relativty/Relativty/ressources/img/headset.jpg

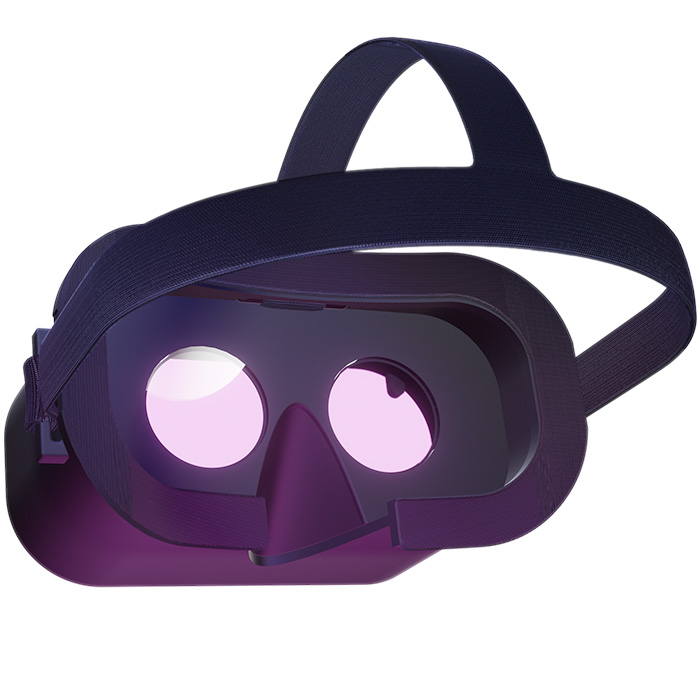
ressources/img/headset.jpg
