relativty/Relativty/Relativty_Driver/include/Relativty_HMDDriver.hpp

// Copyright (C) 2020  Max Coutte, Gabriel Combe
// Copyright (C) 2020  Relativty.com
//
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
#pragma once
#include <thread>
#include <atomic>
#include <WinSock2.h>
#include "hidapi/hidapi.h"
#include "openvr_driver.h"
#include "Relativty_components.h"
#include "Relativty_base_device.h"

namespace Relativty {
	class HMDDriver : public RelativtyDevice<false>
	{
	public:
		HMDDriver(std::string myserial);
		~HMDDriver() = default;

		void frameUpdate();
		inline void setProperties();

		// Inherited from RelativtyDevice, to be overridden
		virtual vr::EVRInitError Activate(uint32_t unObjectId);
		virtual void Deactivate();

	private:
		int32_t m_iPid;
		int32_t m_iVid;

		bool m_bIMUpktIsDMP;

		float SecondsFromVsyncToPhotons;
		float DisplayFrequency;
		float IPD;
		float HeadToEyeDepth;

		vr::DriverPose_t lastPose = {0};
		hid_device* handle;

		std::atomic<float> quat[4];
		std::atomic<bool> retrieve_quaternion_isOn = false;
		std::atomic<bool> new_quaternion_avaiable = false;

		std::atomic<float> qconj[4] = {1, 0, 0, 0};
		void calibrate_quaternion();

		std::thread retrieve_quaternion_thread_worker;
		void retrieve_device_quaternion_packet_threaded();

		std::atomic<float> vector_xyz[3];
		std::atomic<bool> retrieve_vector_isOn = false;
		std::atomic<bool> new_vector_avaiable = false;
		bool start_tracking_server = false;
		SOCKET sock, sock_receive;
		float upperBound;
		float lowerBound;

		float normalizeMinX;
		float normalizeMinY;
		float normalizeMinZ;

		float normalizeMaxX;
		float normalizeMaxY;
		float normalizeMaxZ;

		float scalesCoordinateMeterX;
		float scalesCoordinateMeterY;
		float scalesCoordinateMeterZ;

		float offsetCoordinateX;
		float offsetCoordinateY;
		float offsetCoordinateZ;

		std::atomic<bool> serverNotReady = true;
		std::thread retrieve_vector_thread_worker;
		void retrieve_client_vector_packet_threaded();

		std::thread update_pose_thread_worker;
		void update_pose_threaded();

		std::string PyPath;
		std::thread startPythonTrackingClient_worker;
	};
}
